aa483680845-dev/Open_Arm_Mini/SW_model/Second_edition/DM4340.SLDASM

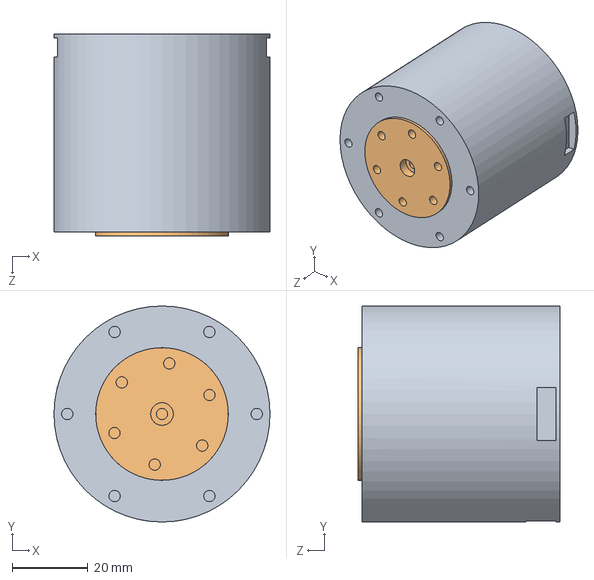
[picture p2: CAD file, 2026-05-10]
SW_model/Second_edition/DM4340.SLDASM
57.0 x 57.0 x 53.2 mm
DM4340转子
DM4340定子
