aa483680845-dev/Open_Arm_Mini/SW_model/First_edition/SLDPRT/robot_1.SLDASM

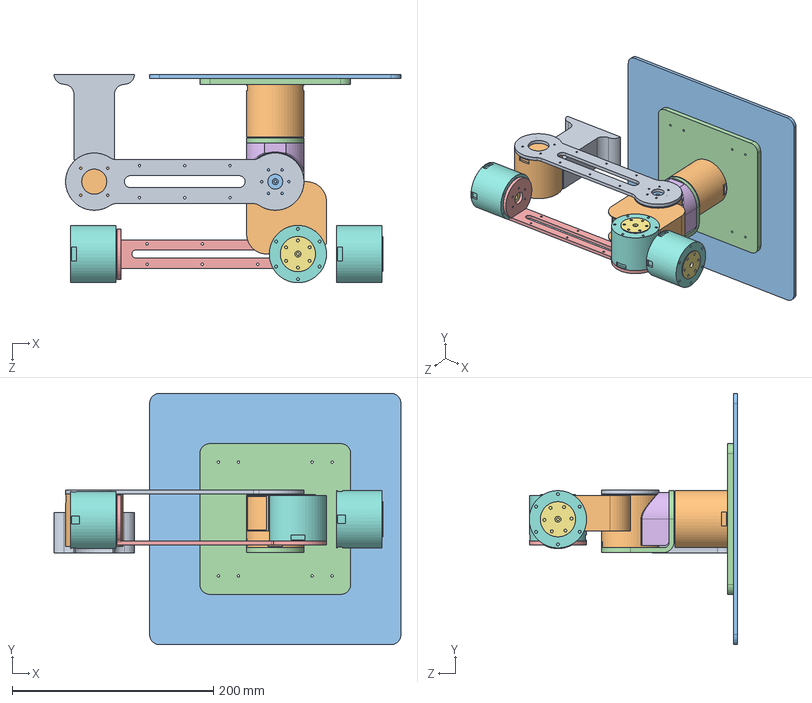
[picture p3: CAD file, 2026-04-25]
SW_model/First_edition/SLDPRT/robot_1.SLDASM
345.0 x 250.0 x 207.3 mm
12轴连接件
DM4340转子 x 3
DM4340定子 x 3
23连杆
DM4310定子 x 3
DM4310转子 x 3
12轴垫片
34轴连杆_改进版_2
底座
大底座
15轴垫块
3轴垫块
