aa483680845-dev/Open_Arm_Mini/SW_model/Second_edition/robot_1.SLDASM

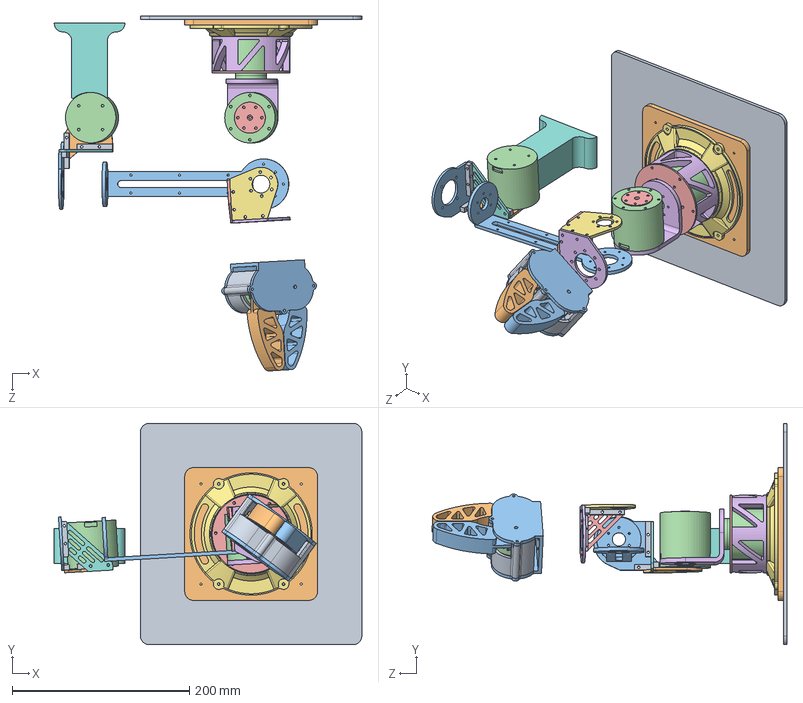
[picture p4: CAD file, 2026-05-10]
SW_model/Second_edition/robot_1.SLDASM
347.4 x 250.0 x 400.7 mm
12轴连接件
DM4340转子 x 3
DM4340定子 x 3
34轴连杆_改进版_2
底座
大底座
3轴垫块
大Y固定下连接垫块
铜柱固定件
电机固定件
电机垫块 x 2
R电机固定
P电机固定
6 6 40 M3 x 6
P R连接件
末P连接板
末R固定板
P R连接件2
末端爪子电机
末端夹爪固定件
齿轮17×2
从动齿轮17×2
轴承垫块
轴承10 15 4
轴承压块
轴承上压块
4 25铜柱
夹爪
夹爪2
外壳
