aa483680845-dev/Open_Arm_Mini/ros2_package/robot_description/meshes/link_6.STL

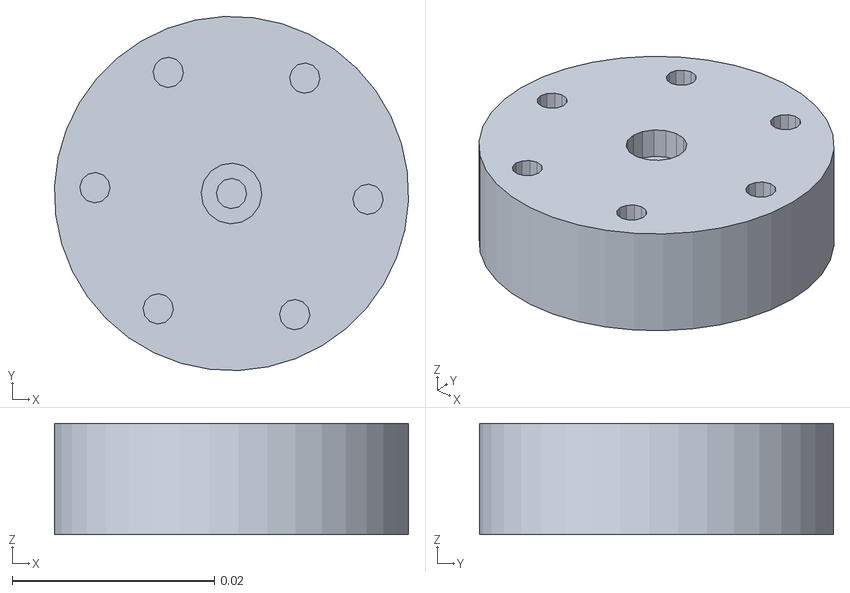
[picture p18: CAD file, 2026-04-25]
ros2_package/robot_description/meshes/link_6.STL
0.035 x 0.035 x 0.011
