aa483680845-dev/Open_Arm_Mini/SW_model/First_edition/STEP/大底座.STEP

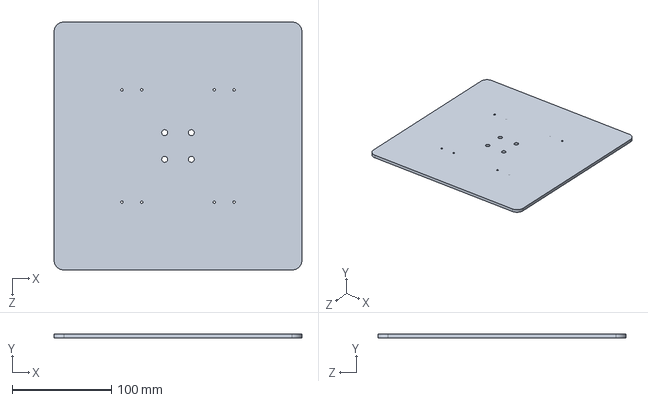
[picture p19: CAD file, 2026-04-25]
SW_model/First_edition/STEP/大底座.STEP
250.0 x 4.00 x 250.0 mm
