aa483680845-dev/Open_Arm_Mini/SW_model/Second_edition/电机垫块.SLDPRT

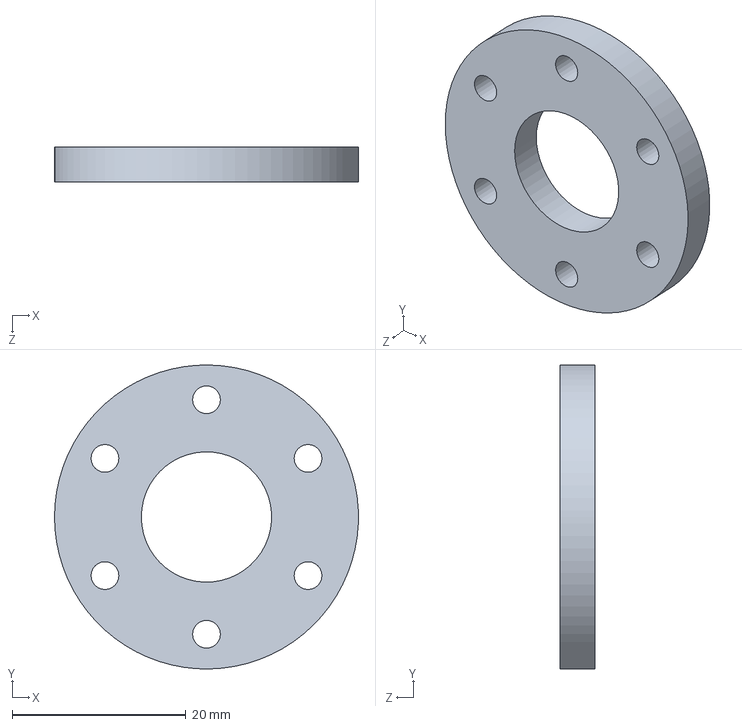
[picture p20: CAD file, 2026-05-10]
SW_model/Second_edition/电机垫块.SLDPRT
35.0 x 35.0 x 4.00 mm
