aa483680845-dev/Open_Arm_Mini/ros2_package/robot_description/meshes/link_4.STL

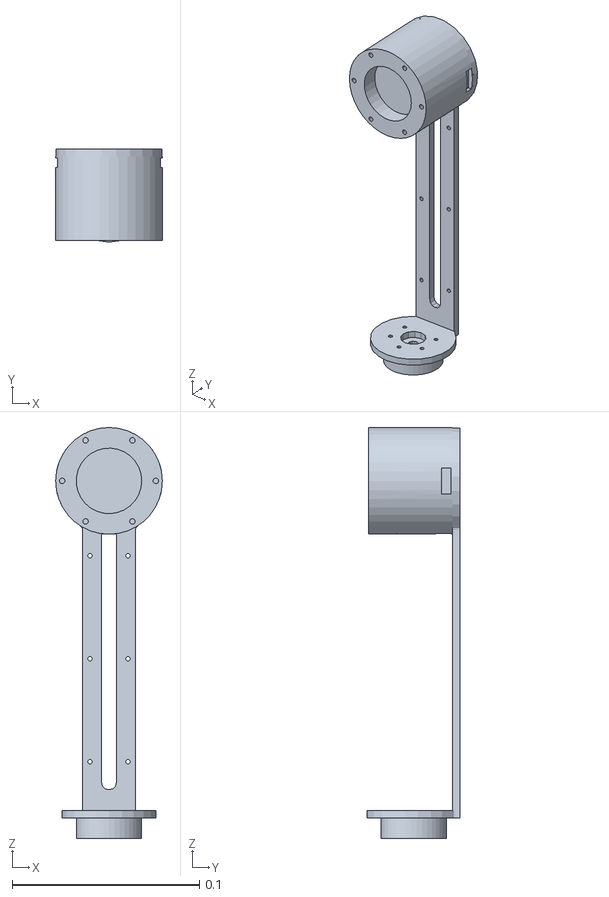
[picture p21: CAD file, 2026-04-25]
ros2_package/robot_description/meshes/link_4.STL
0.057 x 0.0499 x 0.219
