aa483680845-dev/Open_Arm_Mini/SW_model/First_edition/STEP/56轴连接件.STEP

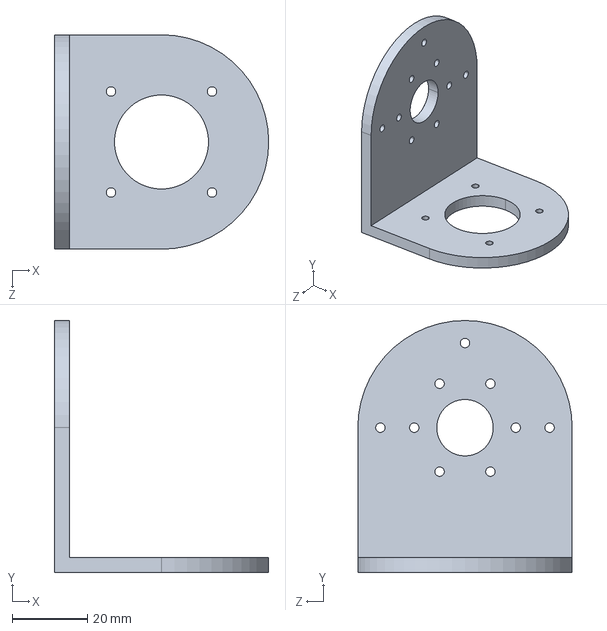
[picture p22: CAD file, 2026-04-25]
SW_model/First_edition/STEP/56轴连接件.STEP
57.0 x 67.0 x 57.0 mm
