aa483680845-dev/Open_Arm_Mini/SW_model/Second_edition/R电机固定.SLDPRT

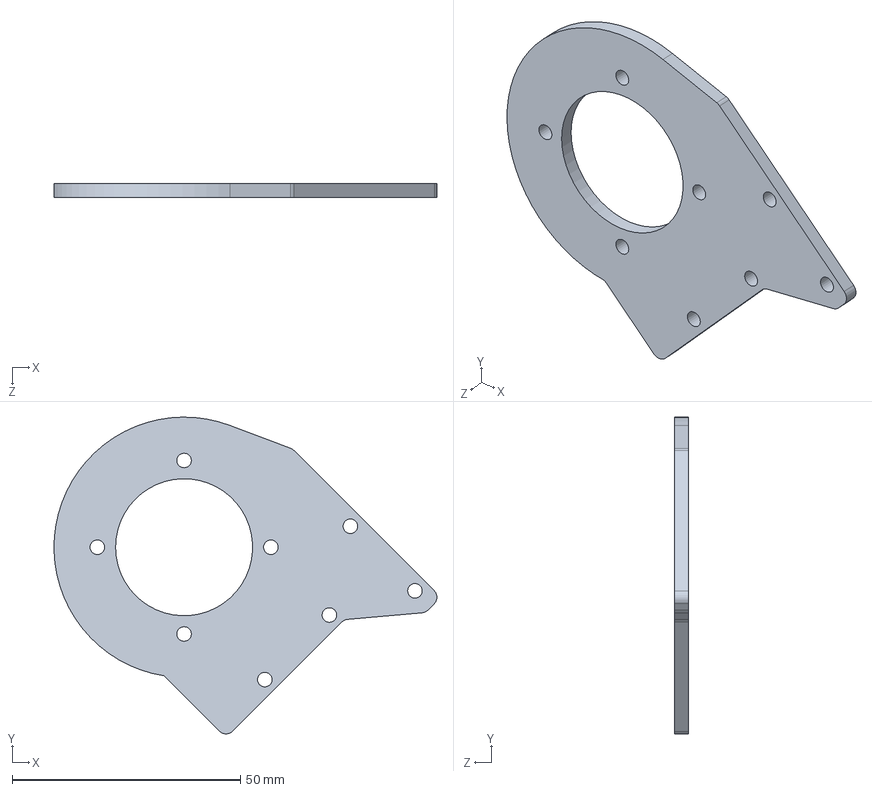
[picture p23: CAD file, 2026-05-10]
SW_model/Second_edition/R电机固定.SLDPRT
83.9 x 69.4 x 3.00 mm
