aa483680845-dev/Open_Arm_Mini/ros2_package/robot_description/meshes/link_5.STL

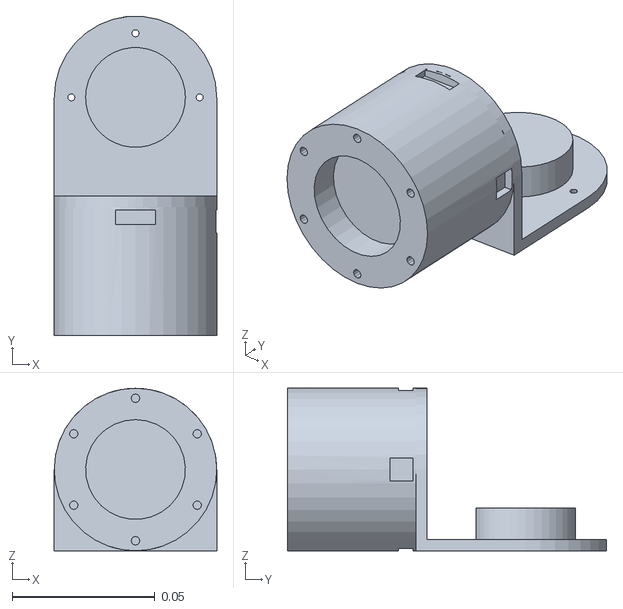
[picture p24: CAD file, 2026-04-25]
ros2_package/robot_description/meshes/link_5.STL
0.057 x 0.112 x 0.057
