aa483680845-dev/Open_Arm_Mini/SW_model/First_edition/STEP/34轴连接件.STEP

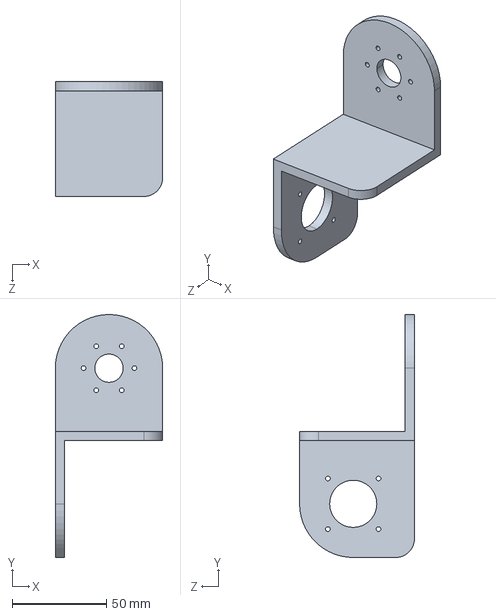
[picture p25: CAD file, 2026-04-25]
SW_model/First_edition/STEP/34轴连接件.STEP
57.0 x 129.0 x 61.0 mm
