aa483680845-dev/Open_Arm_Mini/ros2_package/robot_description/meshes/base_link.STL

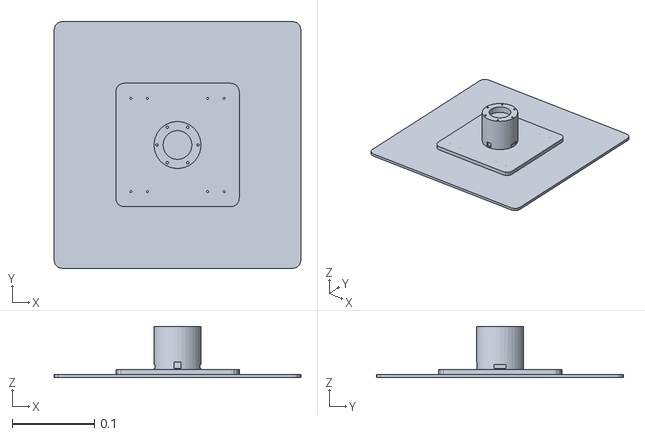
[picture p26: CAD file, 2026-04-25]
ros2_package/robot_description/meshes/base_link.STL
0.3 x 0.3 x 0.0623
