aa483680845-dev/Open_Arm_Mini/SW_model/First_edition/STEP/34轴连杆.STEP

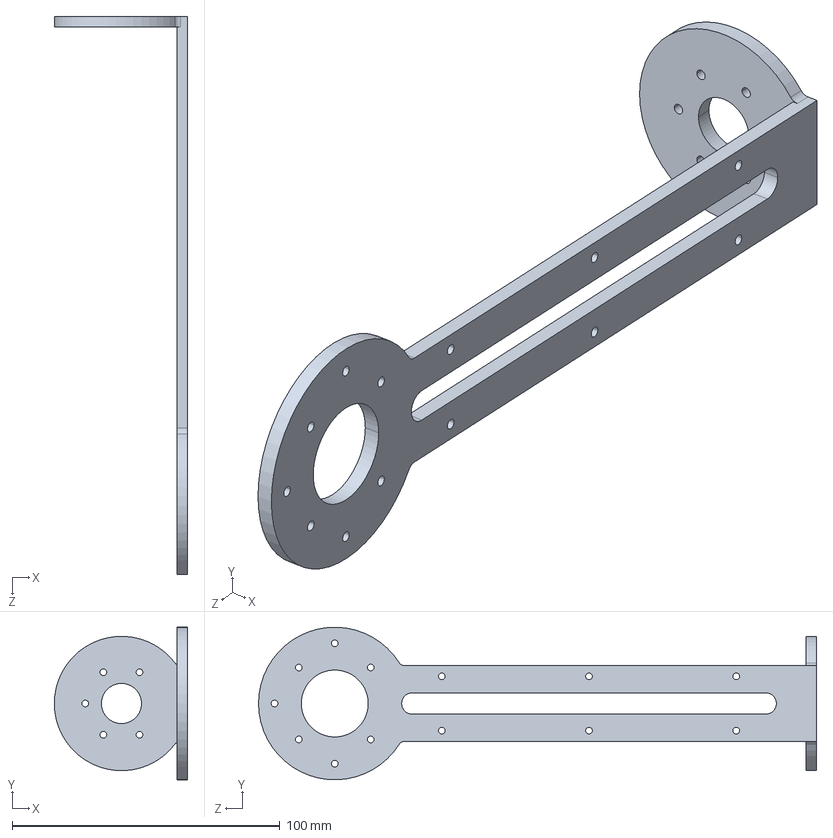
[picture p27: CAD file, 2026-04-25]
SW_model/First_edition/STEP/34轴连杆.STEP
49.9 x 57.0 x 208.5 mm
