aa483680845-dev/Open_Arm_Mini/SW_model/Second_edition/外壳.SLDPRT

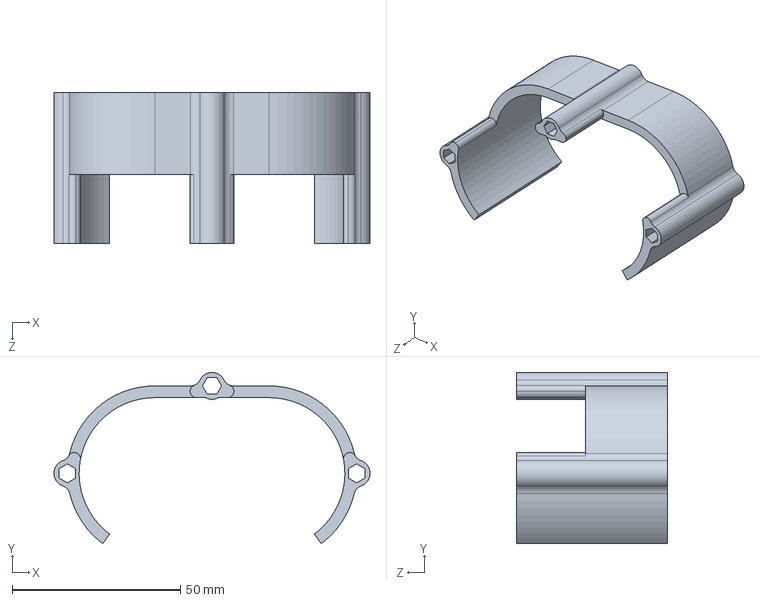
[picture p28: CAD file, 2026-05-10]
SW_model/Second_edition/外壳.SLDPRT
93.9 x 50.9 x 45.0 mm
