aa483680845-dev/Open_Arm_Mini/SW_model/Second_edition/6 6 40 M3.SLDPRT

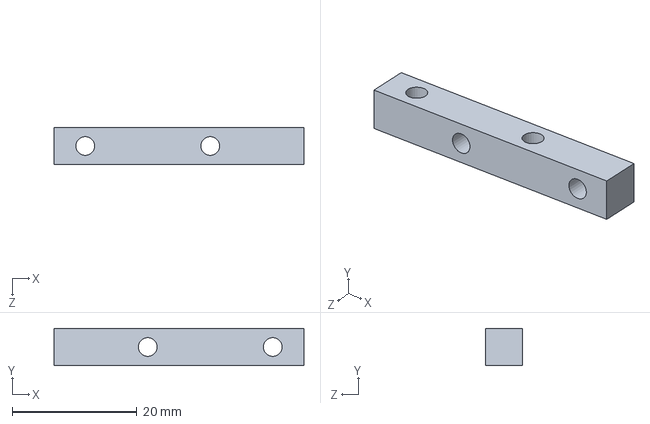
[picture p29: CAD file, 2026-05-10]
SW_model/Second_edition/6 6 40 M3.SLDPRT
40.0 x 6.00 x 6.00 mm
