aa483680845-dev/Open_Arm_Mini/SW_model/Second_edition/末R固定板.SLDPRT

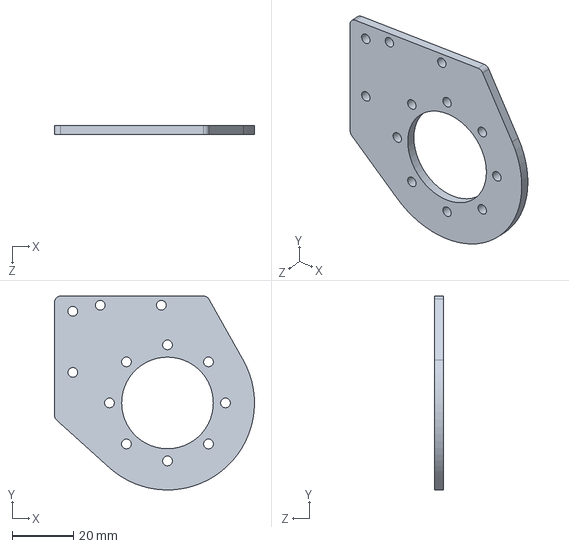
[picture p30: CAD file, 2026-05-10]
SW_model/Second_edition/末R固定板.SLDPRT
65.5 x 63.5 x 3.00 mm
