aa483680845-dev/Open_Arm_Mini/SW_model/Second_edition/轴承10 15 4.SLDPRT

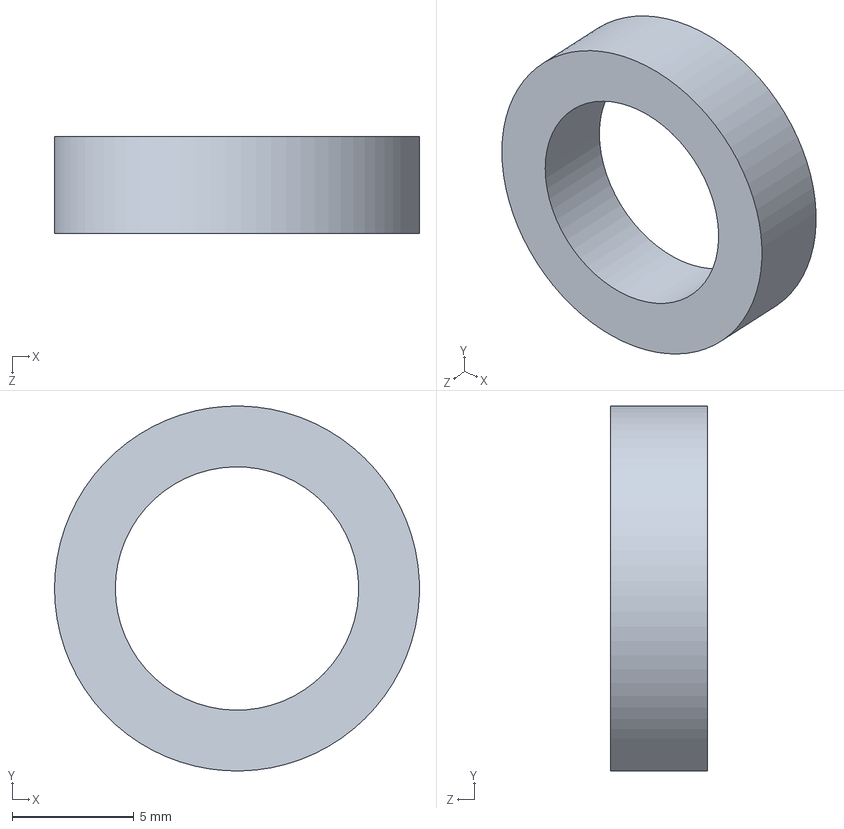
[picture p31: CAD file, 2026-05-10]
SW_model/Second_edition/轴承10 15 4.SLDPRT
15.0 x 15.0 x 4.00 mm
