aa483680845-dev/Open_Arm_Mini/SW_model/Second_edition/P电机固定.SLDPRT

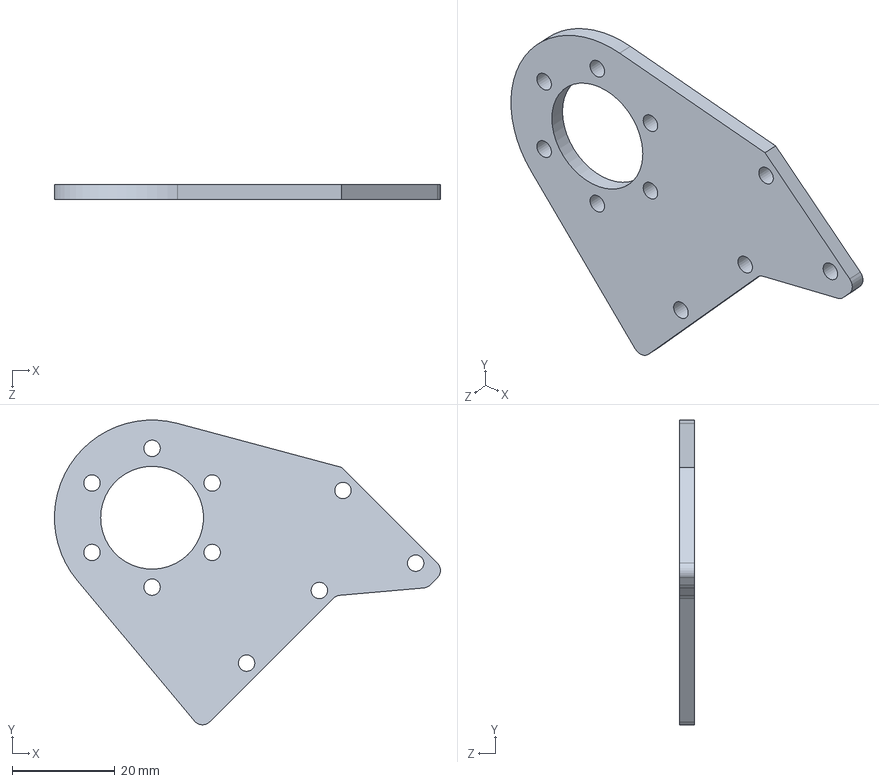
[picture p32: CAD file, 2026-05-10]
SW_model/Second_edition/P电机固定.SLDPRT
75.1 x 59.3 x 3.00 mm
