aa483680845-dev/Open_Arm_Mini/SW_model/Second_edition/从动齿轮17×2 .SLDPRT

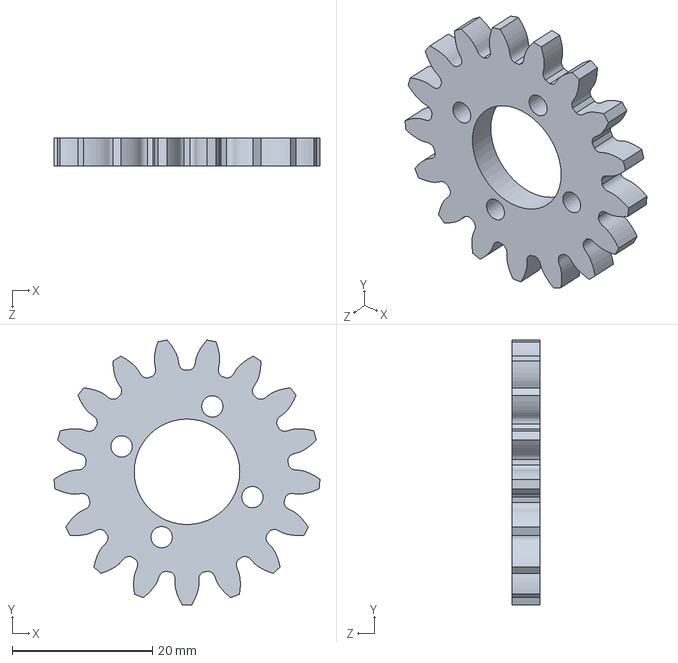
[picture p33: CAD file, 2026-05-10]
SW_model/Second_edition/从动齿轮17×2 .SLDPRT
37.9 x 37.8 x 4.00 mm
