aa483680845-dev/Open_Arm_Mini/SW_model/Second_edition/P R连接件2.SLDPRT

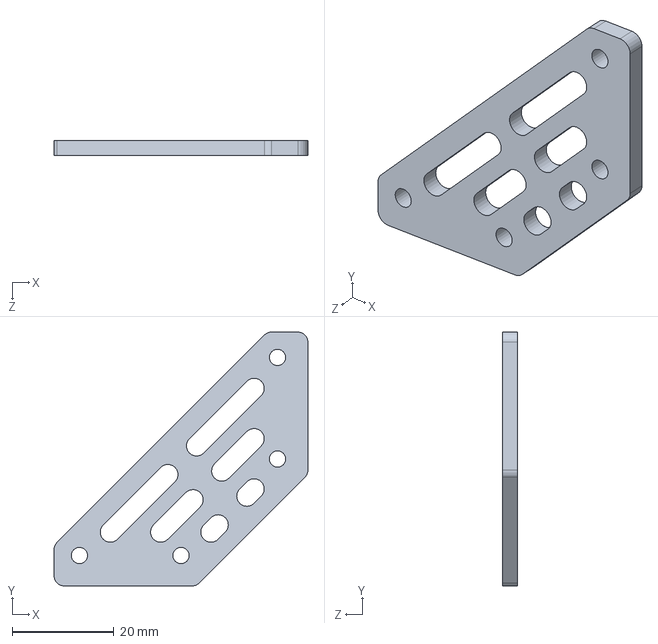
[picture p35: CAD file, 2026-05-10]
SW_model/Second_edition/P R连接件2.SLDPRT
50.0 x 50.0 x 3.00 mm
