aa483680845-dev/Open_Arm_Mini/SW_model/Second_edition/夹爪2.SLDPRT

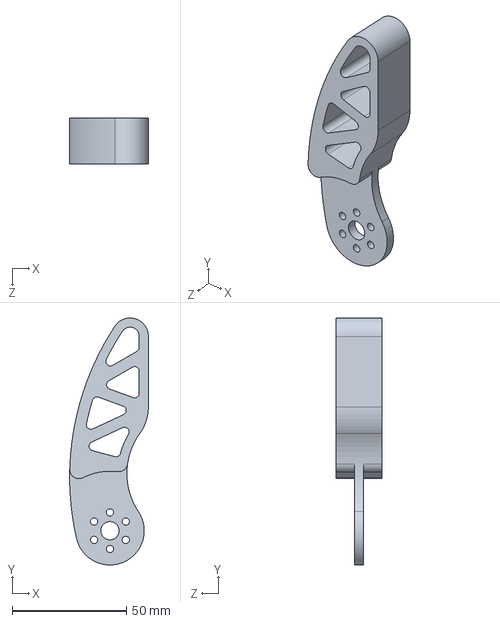
[picture p36: CAD file, 2026-05-10]
SW_model/Second_edition/夹爪2.SLDPRT
34.4 x 108.0 x 20.0 mm
