aa483680845-dev/Open_Arm_Mini/SW_model/Second_edition/P R连接件.SLDPRT

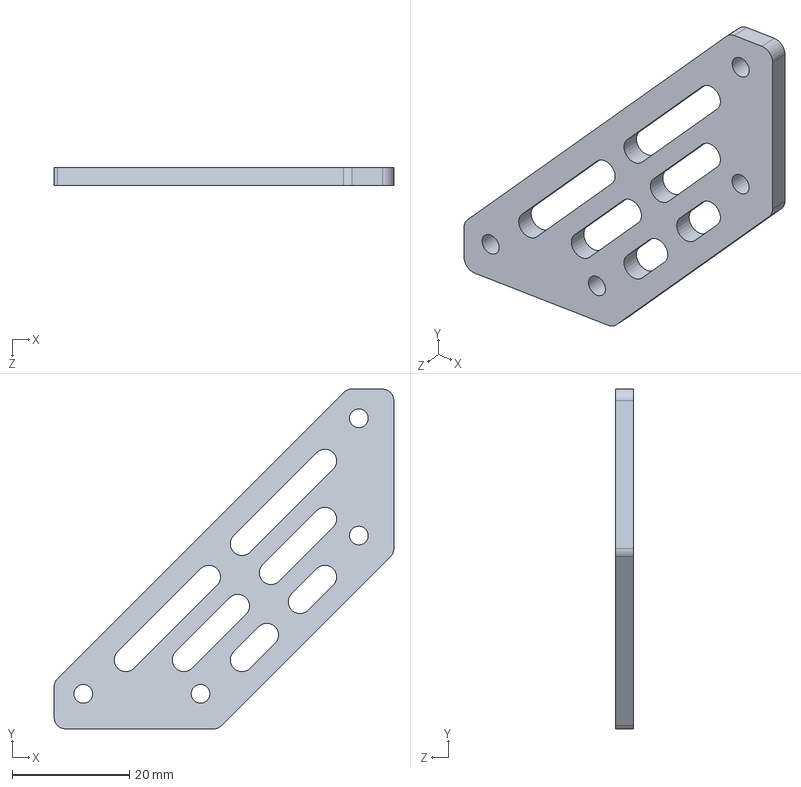
[picture p37: CAD file, 2026-05-10]
SW_model/Second_edition/P R连接件.SLDPRT
58.0 x 58.0 x 3.00 mm
