aa483680845-dev/Open_Arm_Mini/SW_model/Second_edition/轴承垫块.SLDPRT

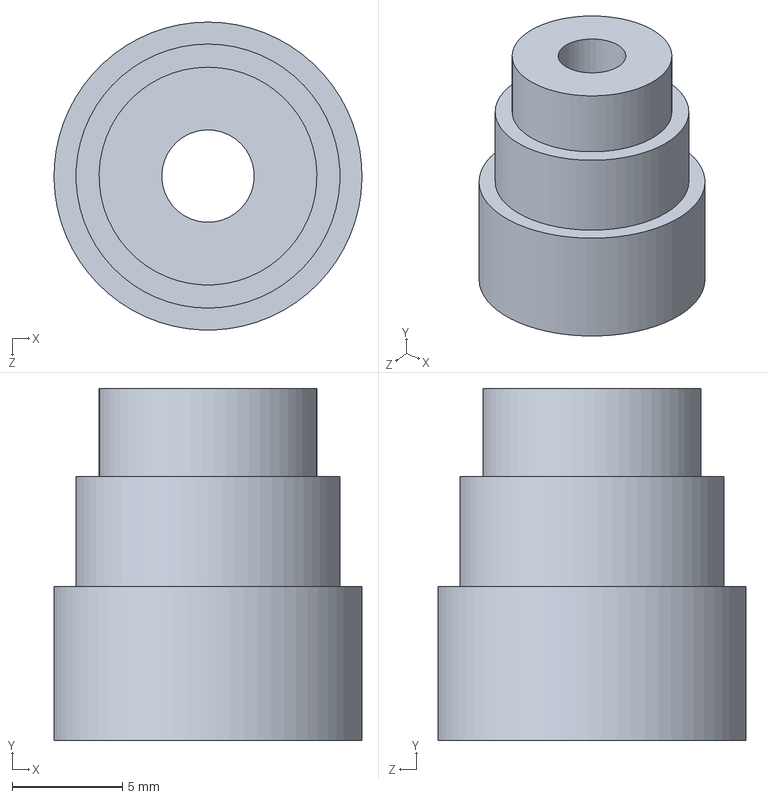
[picture p38: CAD file, 2026-05-10]
SW_model/Second_edition/轴承垫块.SLDPRT
14.0 x 16.0 x 14.0 mm
