aa483680845-dev/Open_Arm_Mini/SW_model/Second_edition/末P连接板.SLDPRT

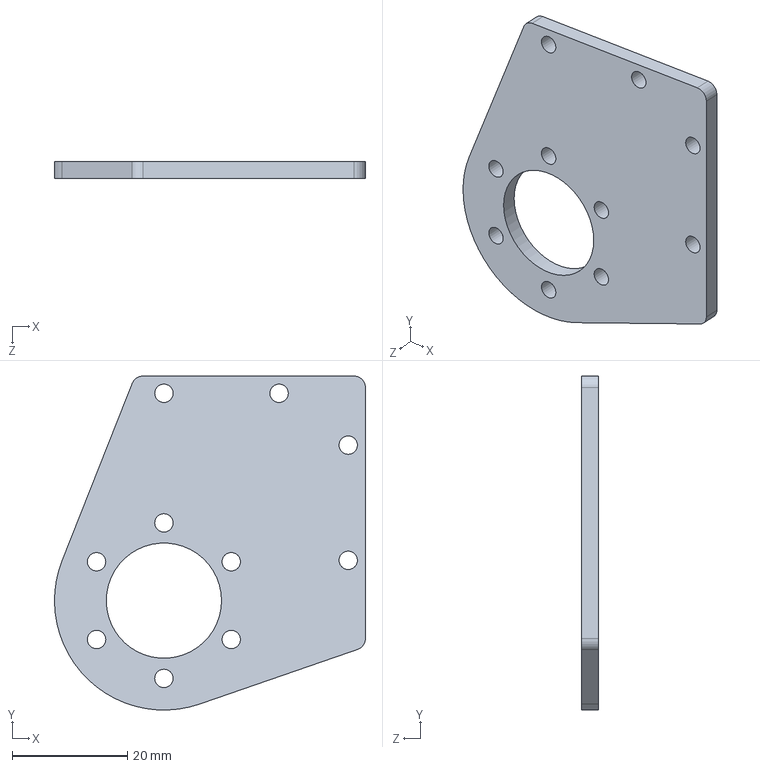
[picture p39: CAD file, 2026-05-10]
SW_model/Second_edition/末P连接板.SLDPRT
54.0 x 58.0 x 3.00 mm
