aa483680845-dev/Open_Arm_Mini/SW_model/Second_edition/大Y固定下连接垫块.SLDPRT

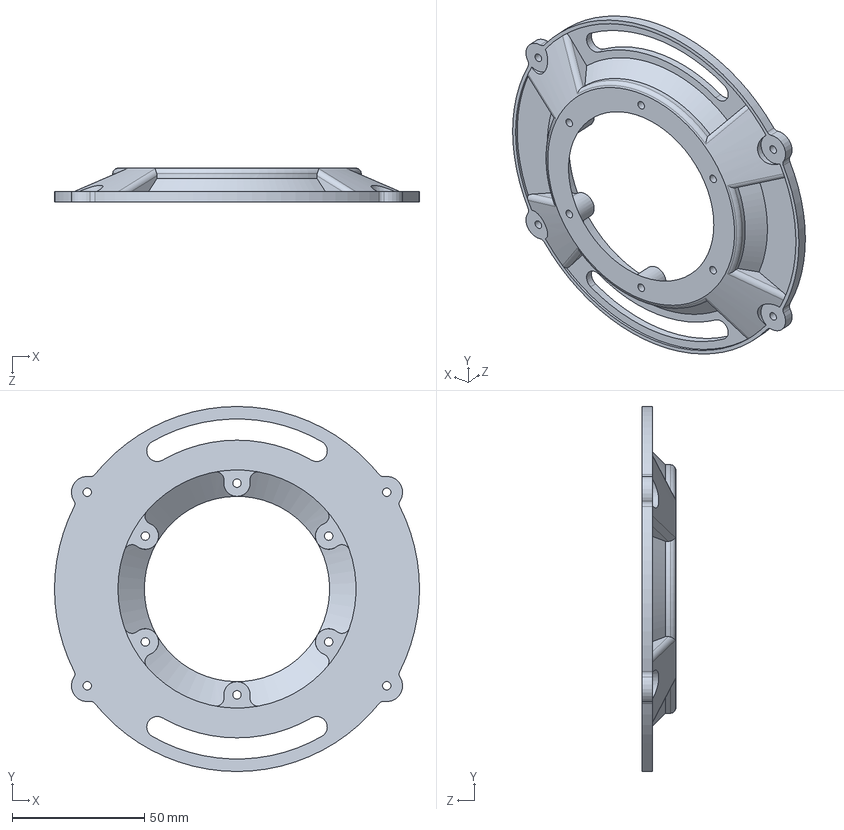
[picture p40: CAD file, 2026-05-10]
SW_model/Second_edition/大Y固定下连接垫块.SLDPRT
138.0 x 138.0 x 13.0 mm
