aa483680845-dev/Open_Arm_Mini/SW_model/Second_edition/4 25铜柱.SLDPRT

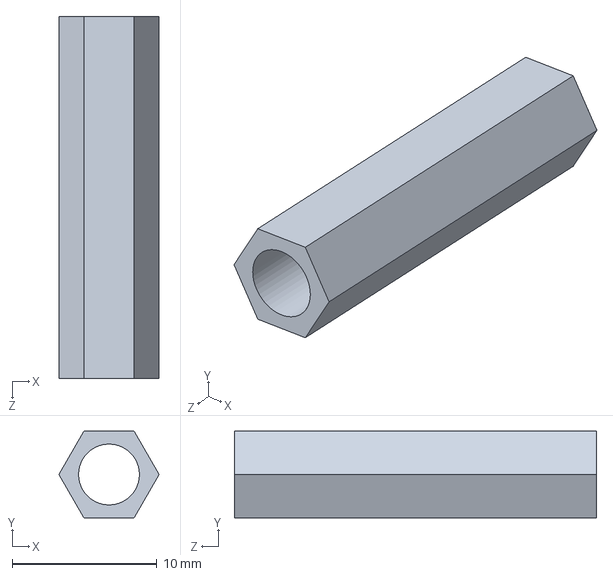
[picture p41: CAD file, 2026-05-10]
SW_model/Second_edition/4 25铜柱.SLDPRT
6.93 x 6.00 x 25.0 mm
