aa483680845-dev/Open_Arm_Mini/SW_model/Second_edition/末端夹爪固定件.SLDPRT

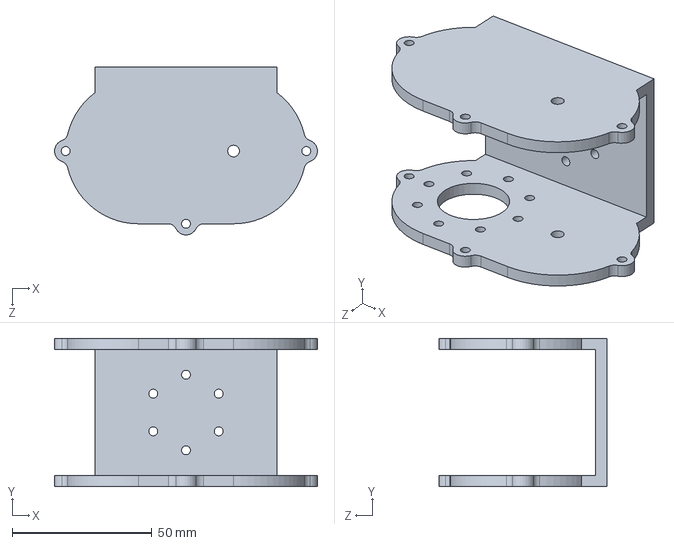
[picture p42: CAD file, 2026-05-10]
SW_model/Second_edition/末端夹爪固定件.SLDPRT
94.0 x 53.0 x 60.0 mm
