aa483680845-dev/Open_Arm_Mini/SW_model/Second_edition/末端爪子电机.SLDPRT

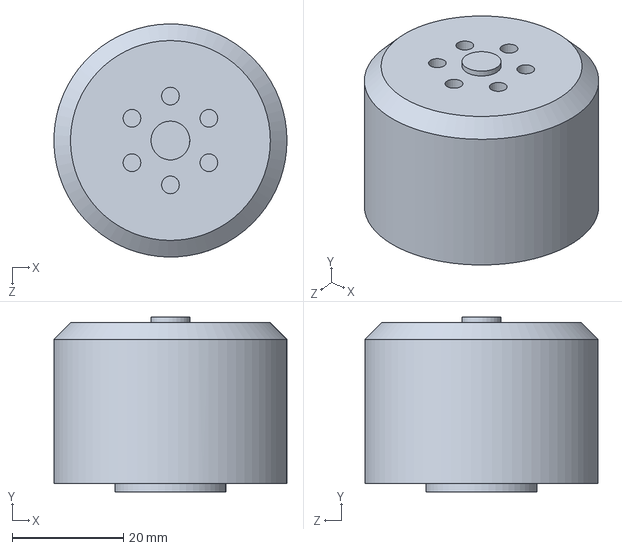
[picture p43: CAD file, 2026-05-10]
SW_model/Second_edition/末端爪子电机.SLDPRT
42.0 x 31.5 x 42.0 mm
