aa483680845-dev/Open_Arm_Mini/SW_model/Second_edition/铜柱固定件.SLDPRT

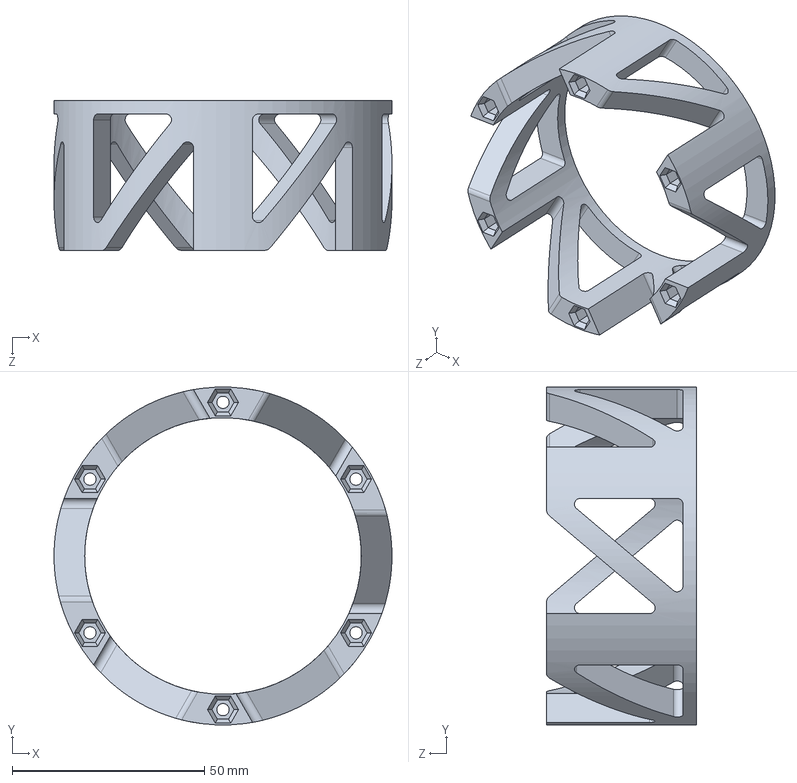
[picture p44: CAD file, 2026-05-10]
SW_model/Second_edition/铜柱固定件.SLDPRT
88.0 x 87.9 x 39.0 mm
