aa483680845-dev/Open_Arm_Mini/SW_model/Second_edition/轴承上压块.SLDPRT

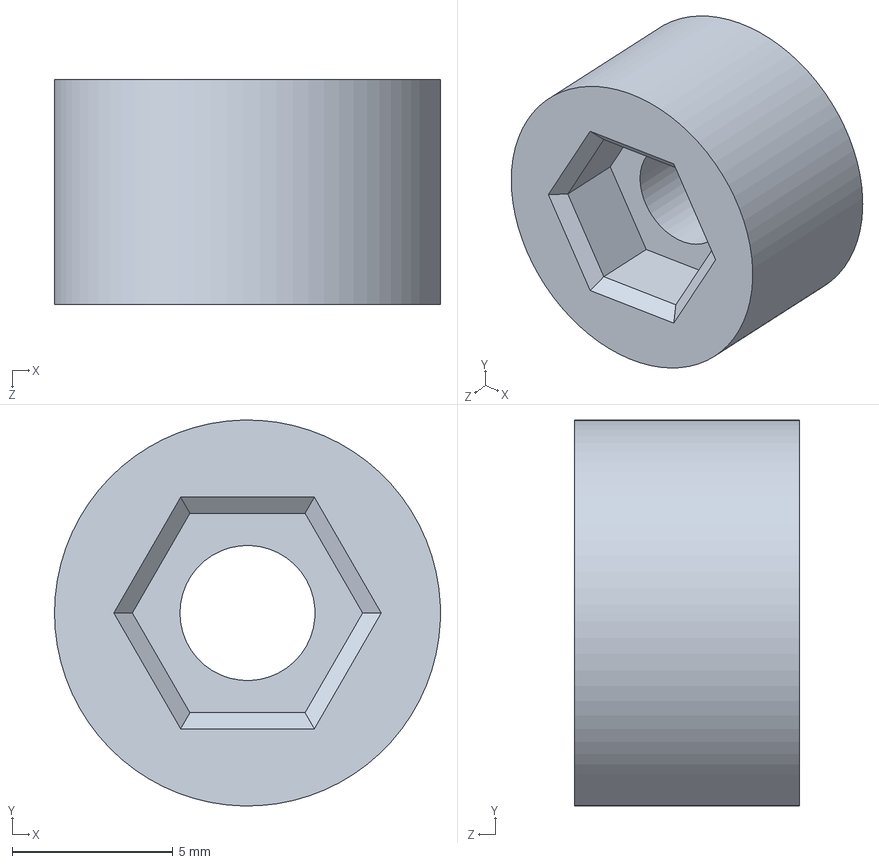
[picture p45: CAD file, 2026-05-10]
SW_model/Second_edition/轴承上压块.SLDPRT
12.0 x 12.0 x 7.00 mm
