aa483680845-dev/Open_Arm_Mini/SW_model/Second_edition/电机固定件.SLDPRT

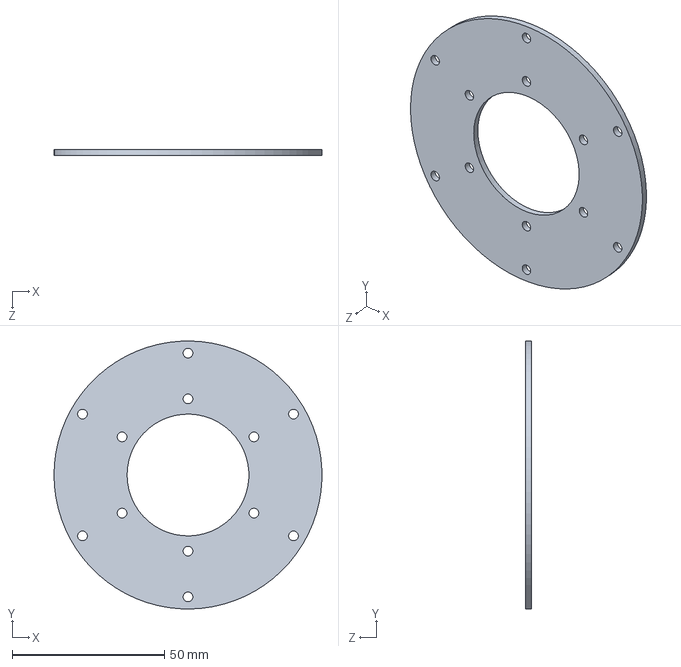
[picture p46: CAD file, 2026-05-10]
SW_model/Second_edition/电机固定件.SLDPRT
88.0 x 88.0 x 2.00 mm
