aa483680845-dev/Open_Arm_Mini/SW_model/Second_edition/12轴垫片.SLDPRT

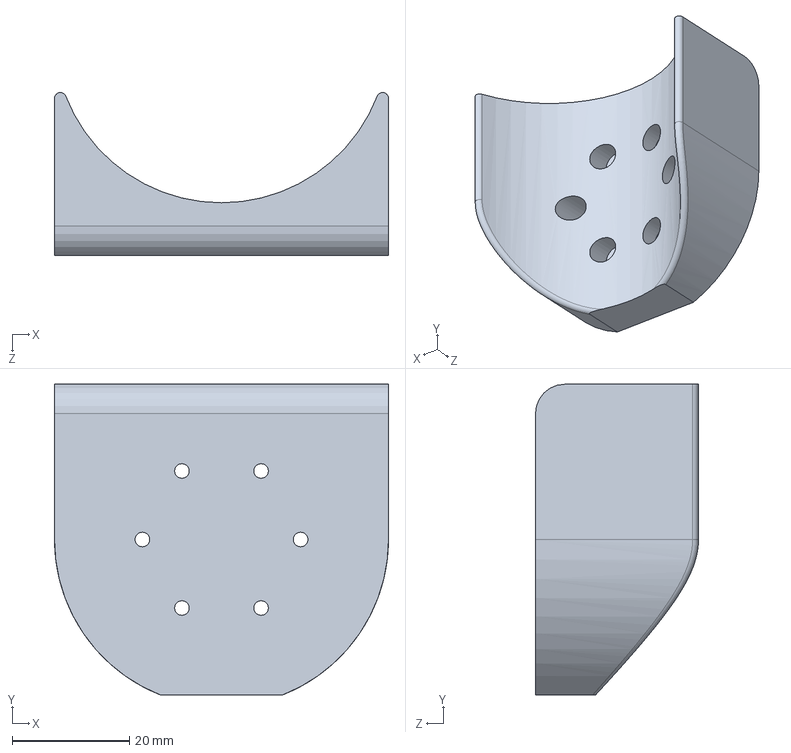
[picture p47: CAD file, 2026-04-25]
SW_model/Second_edition/12轴垫片.SLDPRT
57.0 x 53.0 x 27.8 mm
