aa483680845-dev/Open_Arm_Mini/SW_model/Second_edition/DM4340转子.SLDPRT

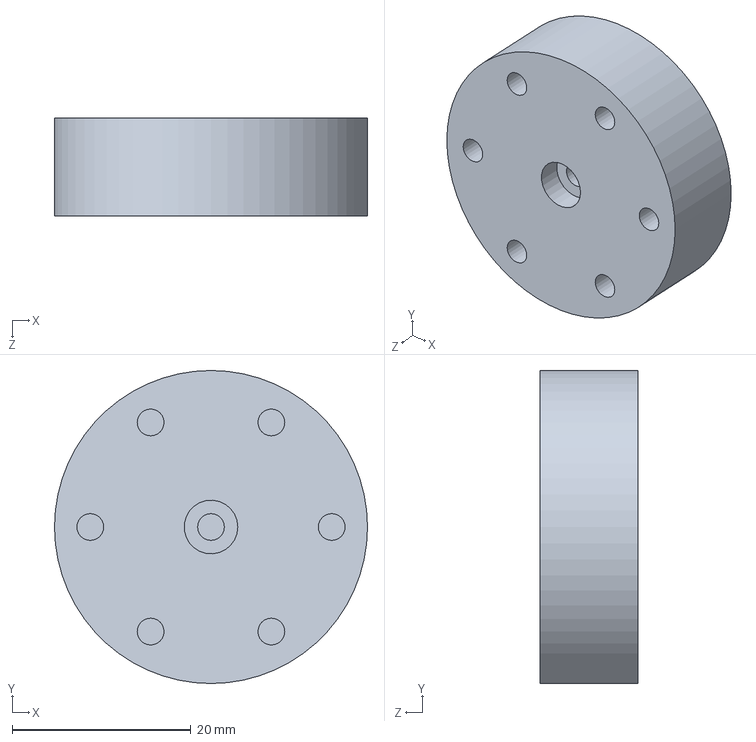
[picture p48: CAD file, 2026-04-25]
SW_model/Second_edition/DM4340转子.SLDPRT
35.0 x 35.0 x 11.0 mm
