aa483680845-dev/Open_Arm_Mini/SW_model/Second_edition/DM4340定子.SLDPRT

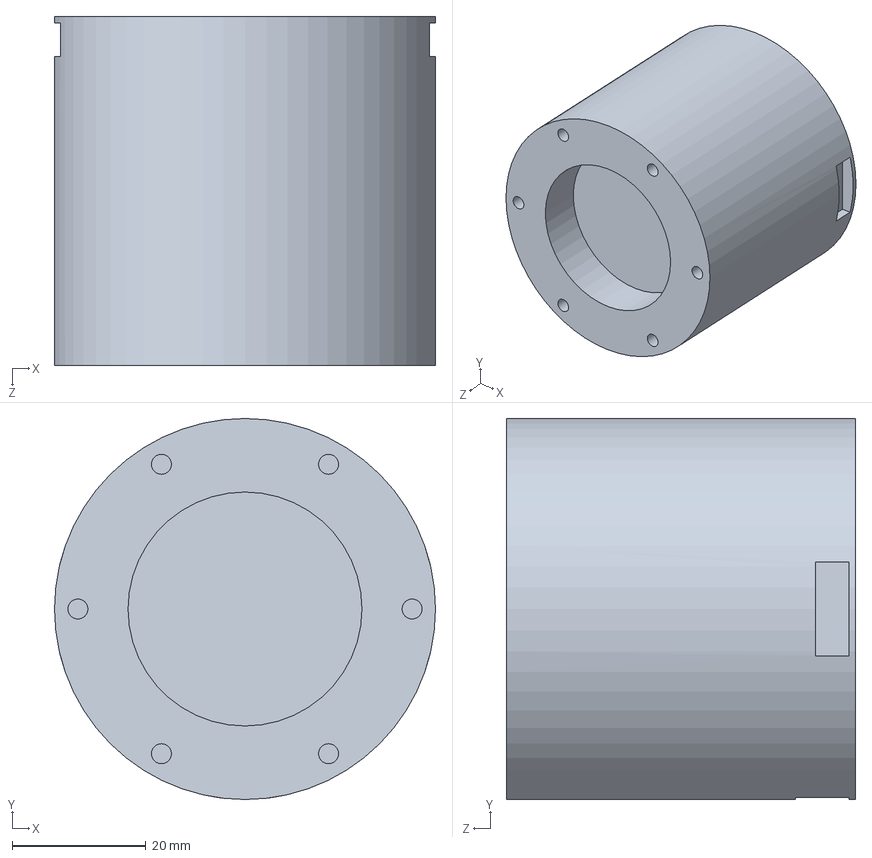
[picture p49: CAD file, 2026-04-25]
SW_model/Second_edition/DM4340定子.SLDPRT
57.0 x 57.0 x 52.2 mm
